NajaBouAkar/Automated-sorting-machine/SW file/Arm 02.SLDPRT

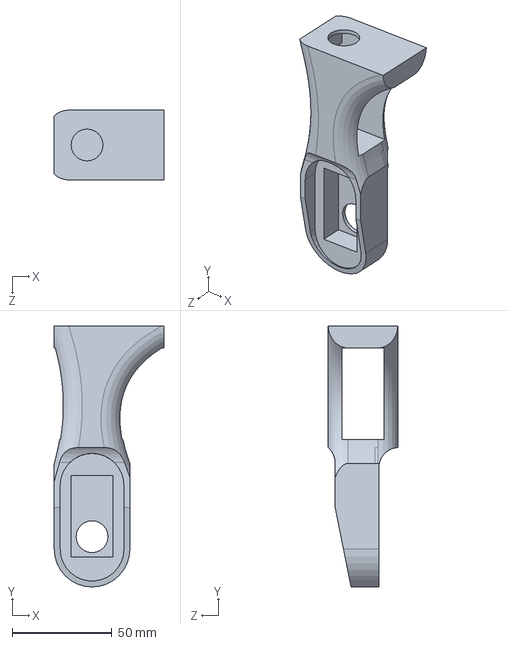
[picture p31: CAD file, 2023-05-10]
SW file/Arm 02.SLDPRT
55.0 x 131.0 x 35.0 mm
