NajaBouAkar/Automated-sorting-machine/SW file/Gripper/Gripper 1 v2.SLDPRT

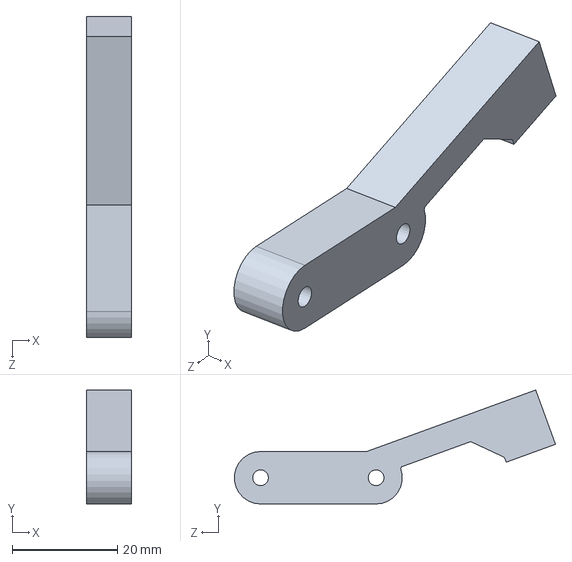
[picture p32: CAD file, 2023-05-10]
SW file/Gripper/Gripper 1 v2.SLDPRT
8.50 x 21.7 x 61.1 mm
