NajaBouAkar/Automated-sorting-machine/SW file/Base_r1.SLDPRT

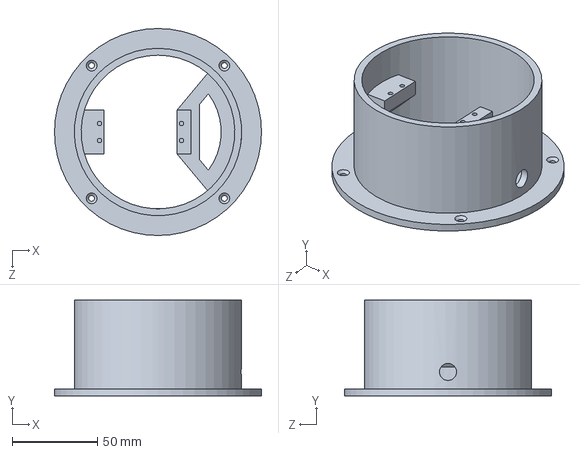
[picture p33: CAD file, 2023-05-10]
SW file/Base_r1.SLDPRT
121.2 x 56.0 x 121.2 mm
