NajaBouAkar/Automated-sorting-machine/SW file/Waist_r1.SLDPRT

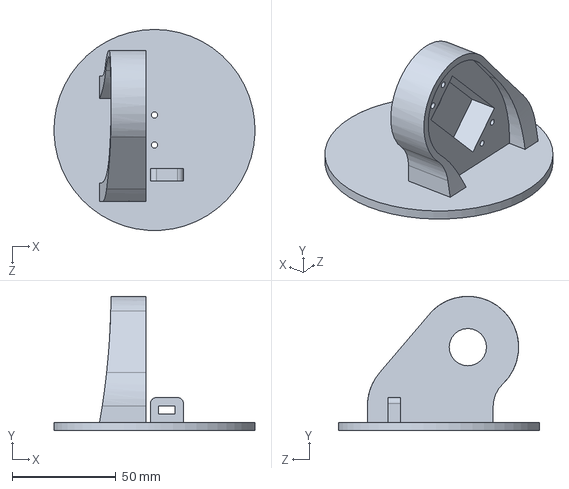
[picture p34: CAD file, 2023-05-10]
SW file/Waist_r1.SLDPRT
97.0 x 64.8 x 97.0 mm
