NajaBouAkar/Automated-sorting-machine/SW file/Test 01.SLDPRT

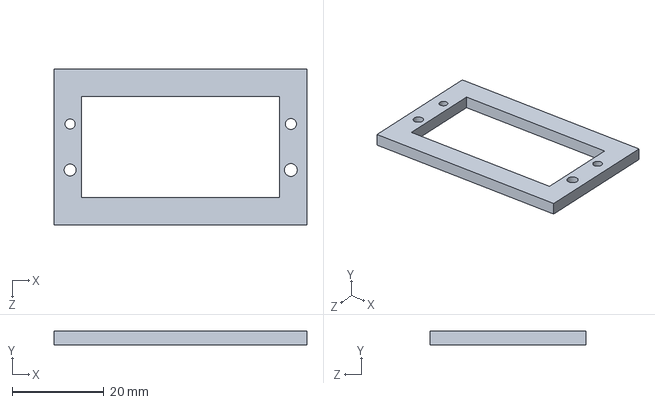
[picture p35: CAD file, 2023-05-10]
SW file/Test 01.SLDPRT
55.0 x 3.00 x 34.0 mm
