NajaBouAkar/Automated-sorting-machine/SW file/Base.SLDPRT

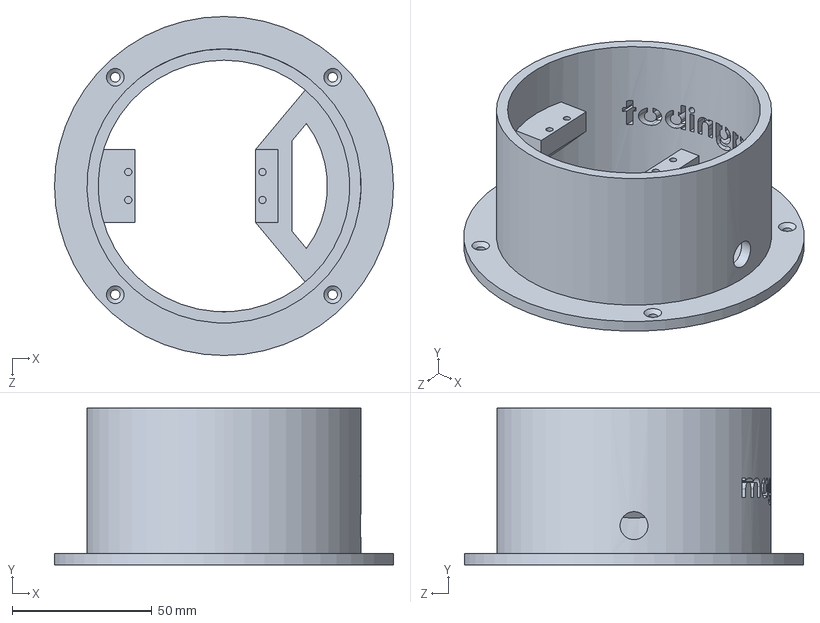
[picture p36: CAD file, 2023-05-10]
SW file/Base.SLDPRT
121.2 x 56.0 x 121.2 mm
